mcranford13/Ps2Plus/hardware/rumble.sch

## KiCad design hardware/rumble.sch (2019-07-23)

Schematic: rumble.sch

Parts:
C1: 10uF
D1: 1N58XX
M: DC Motor
Q1: 2N7000; TO-92_Inline
R1: 1K
R2: 100K
